Arduino-DMX-512-Tester-and-Controller/Arduino-DMX-512-Tester-and-Controller-LCD-20x4-Hardware/Documentacion/Contraste/Contrast PWM.png

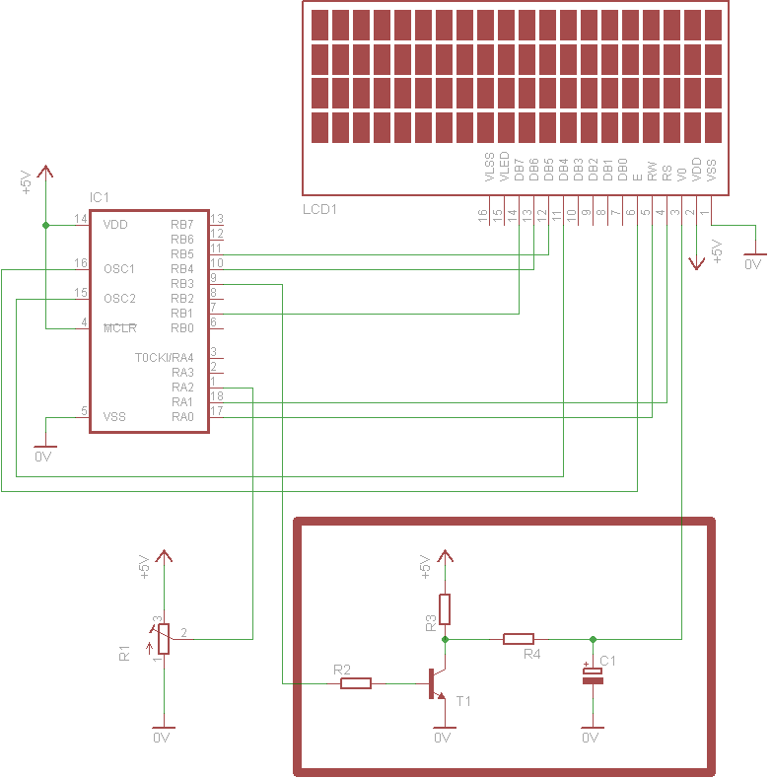
Documentacion/Contraste/Contrast PWM.png
