Arduino-DMX-512-Tester-and-Controller/Arduino-DMX-512-Tester-and-Controller-LCD-20x4-Hardware/Documentacion/DMX Shield/DMXShieldSchema.png

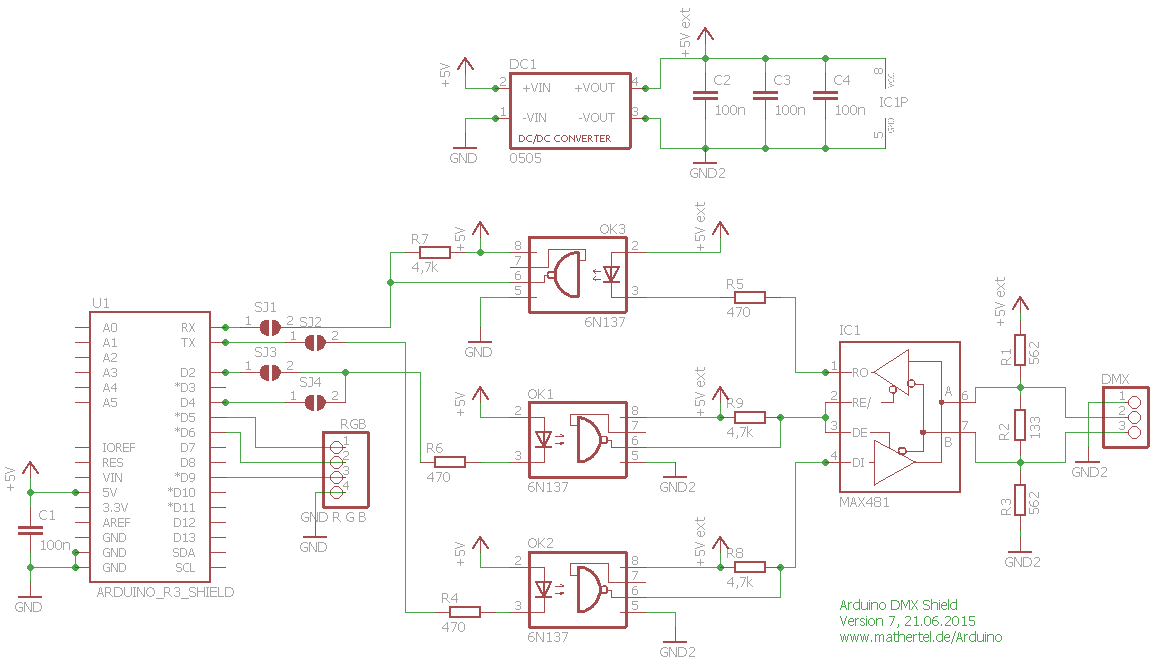
Documentacion/DMX Shield/DMXShieldSchema.png
