Arduino-DMX-512-Tester-and-Controller/Arduino-DMX-512-Tester-and-Controller-LCD-20x4-Hardware/Documentacion/Optoacoplado/DMXShieldSchema.png

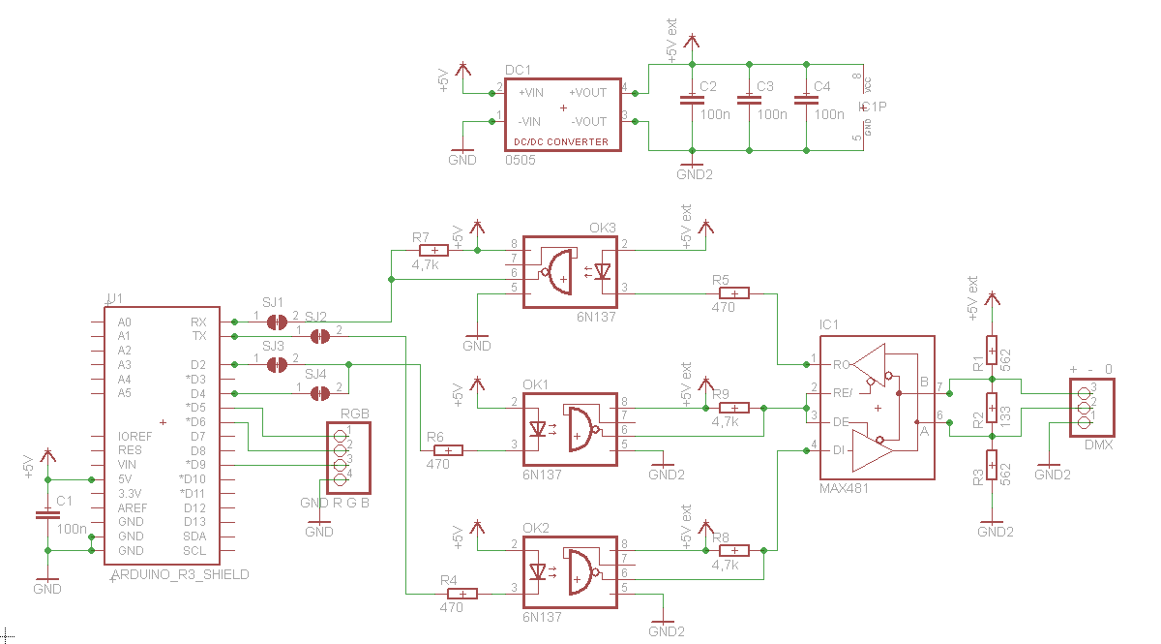
Documentacion/Optoacoplado/DMXShieldSchema.png
