Arduino-DMX-512-Tester-and-Controller/Arduino-DMX-512-Tester-and-Controller-LCD-20x4-Hardware/Documentacion/Teclado/Teclado diagrama.JPG

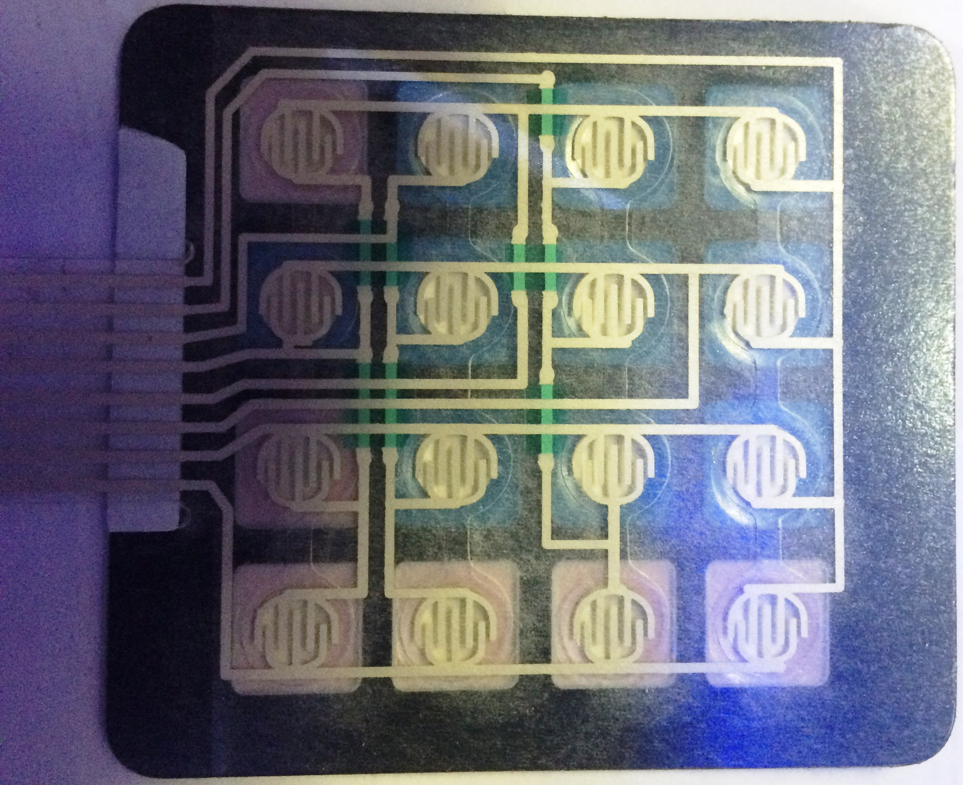
Documentacion/Teclado/Teclado diagrama.JPG
