Arduino-DMX-512-Tester-and-Controller/Arduino-DMX-512-Tester-and-Controller-LCD-20x4-Hardware/Documentacion/Teclado/teclado-4x4-alfanumerico pcb.jpg

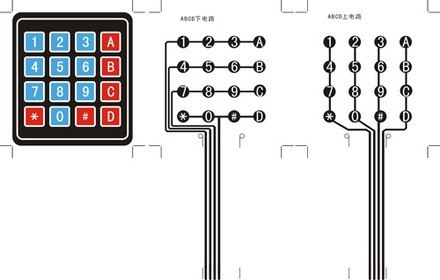
Documentacion/Teclado/teclado-4x4-alfanumerico pcb.jpg
