Arduino-DMX-512-Tester-and-Controller/Arduino-DMX-512-Tester-and-Controller-LCD-20x4-Hardware/Documentacion/Teclado/teclado-4x4-alfanumerico.jpg

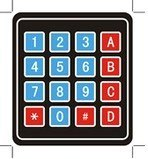
Documentacion/Teclado/teclado-4x4-alfanumerico.jpg
