Arduino-DMX-512-Tester-and-Controller/Arduino-DMX-512-Tester-and-Controller-LCD-20x4-Hardware/Social/Facebook/512 likes.PNG

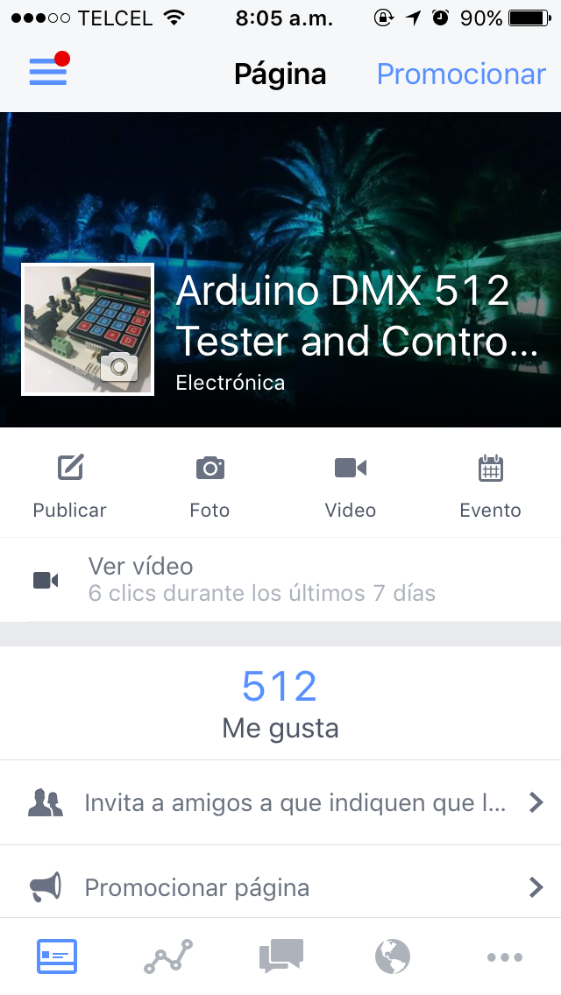
Social/Facebook/512 likes.PNG
