Arduino-DMX-512-Tester-and-Controller/Arduino-DMX-512-Tester-and-Controller-LCD-20x4-Hardware/Social/Hack a Day/HackaDay - Atmel Arduino 2.jpg

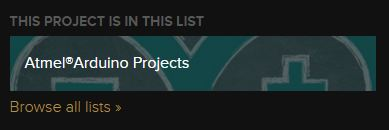
Social/Hack a Day/HackaDay - Atmel Arduino 2.jpg
