Arduino-DMX-512-Tester-and-Controller/Arduino-DMX-512-Tester-and-Controller-LCD-20x4-Hardware/Social/Makers/Alejandro Oteiza - España/18425617_912503192225845_1862307571_n.png

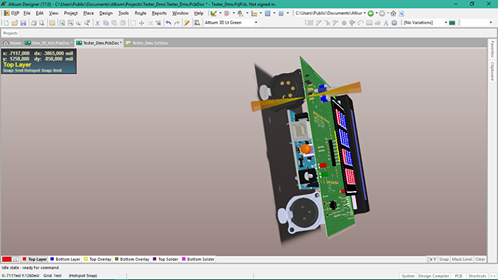
Social/Makers/Alejandro Oteiza - España/18425617_912503192225845_1862307571_n.png
