Arduino-DMX-512-Tester-and-Controller/Arduino-DMX-512-Tester-and-Controller-LCD-20x4-Hardware/Social/Makers/Alejandro Oteiza - España/18426019_912503318892499_1582437020_n.png

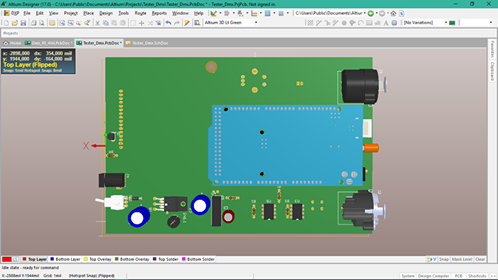
Social/Makers/Alejandro Oteiza - España/18426019_912503318892499_1582437020_n.png
