Arduino-DMX-512-Tester-and-Controller/Arduino-DMX-512-Tester-and-Controller-LCD-20x4-Hardware/Social/Makers/Alejandro Oteiza - España/19478004_941198602689637_196751368_n.jpg

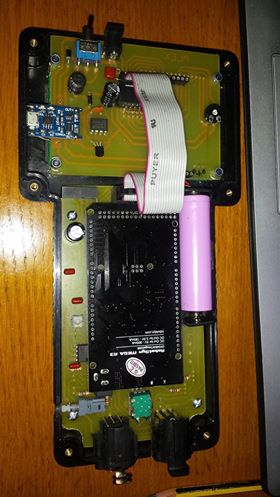
Social/Makers/Alejandro Oteiza - España/19478004_941198602689637_196751368_n.jpg
