Arduino-DMX-512-Tester-and-Controller/Arduino-DMX-512-Tester-and-Controller-LCD-20x4-Hardware/Social/Makers/Alejandro Oteiza - España/IMG_0107.jpg

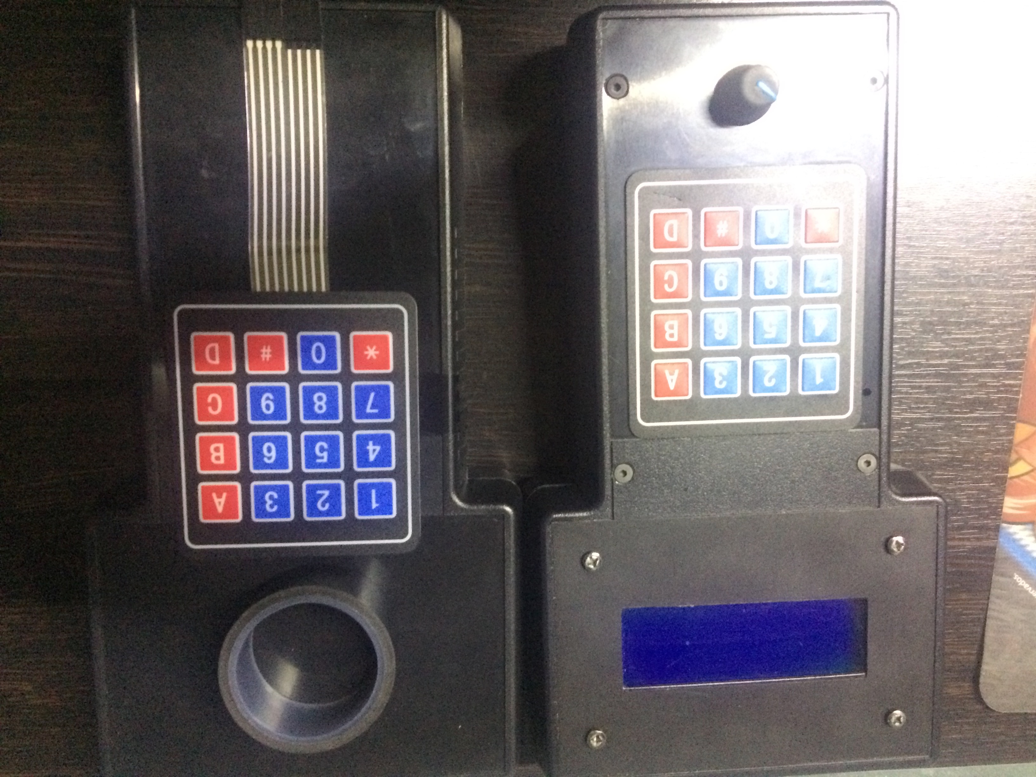
Social/Makers/Alejandro Oteiza - España/IMG_0107.jpg
