Arduino-DMX-512-Tester-and-Controller/Arduino-DMX-512-Tester-and-Controller-LCD-20x4-Hardware/Social/Makers/Magno Campos - Portugal/15725818_1213531232016235_1485832653_o.jpg

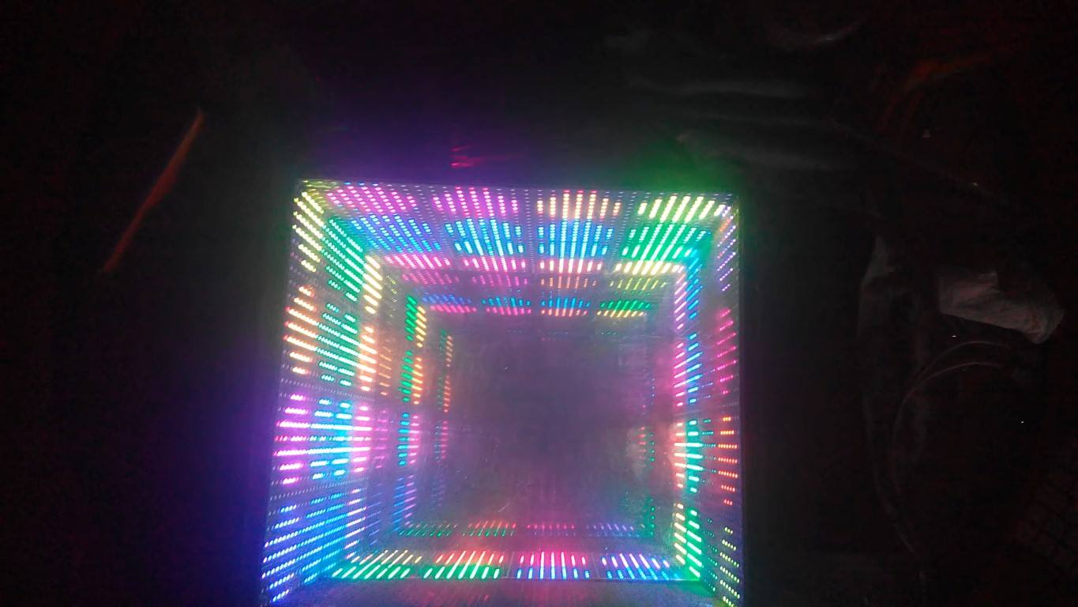
Social/Makers/Magno Campos - Portugal/15725818_1213531232016235_1485832653_o.jpg
