Arduino-DMX-512-Tester-and-Controller/Arduino-DMX-512-Tester-and-Controller-LCD-20x4-Hardware/Social/Makers/Magno Campos - Portugal/15725822_1213531238682901_1854752186_o.jpg

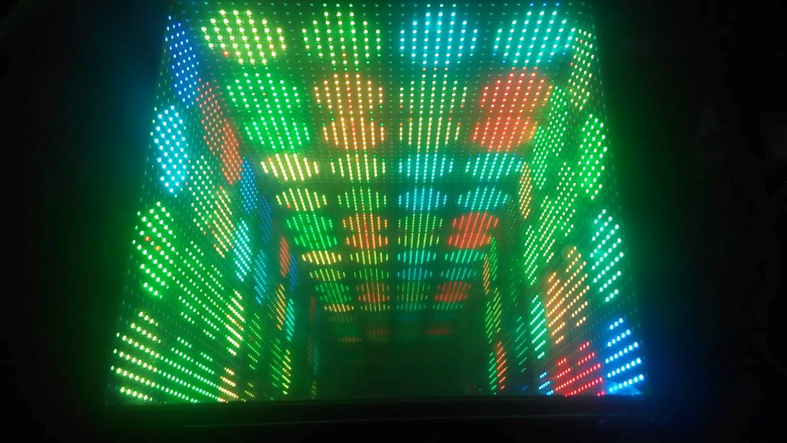
Social/Makers/Magno Campos - Portugal/15725822_1213531238682901_1854752186_o.jpg
