Arduino-DMX-512-Tester-and-Controller/Arduino-DMX-512-Tester-and-Controller-LCD-20x4-Hardware/Social/Makers/Magno Campos - Portugal/15725825_1213540395348652_77643821_o.jpg

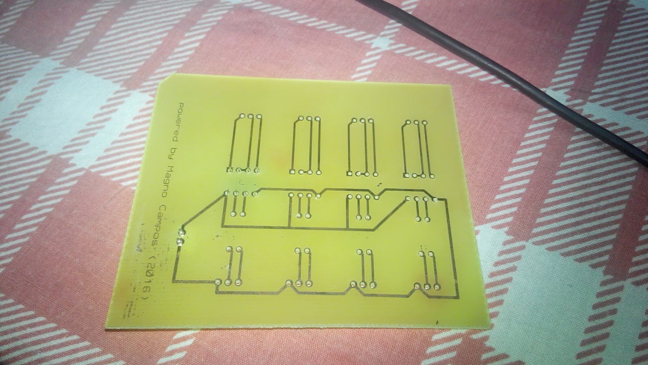
Social/Makers/Magno Campos - Portugal/15725825_1213540395348652_77643821_o.jpg
