Arduino-DMX-512-Tester-and-Controller/Arduino-DMX-512-Tester-and-Controller-LCD-20x4-Hardware/Social/Makers/Magno Campos - Portugal/15731043_1213531242016234_359219261_n.jpg

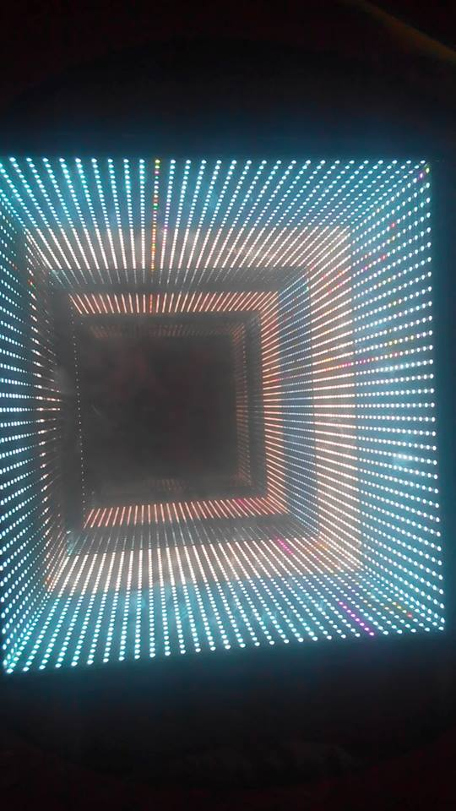
Social/Makers/Magno Campos - Portugal/15731043_1213531242016234_359219261_n.jpg
