Arduino-DMX-512-Tester-and-Controller/Arduino-DMX-512-Tester-and-Controller-LCD-20x4-Hardware/Social/Makers/Magno Campos - Portugal/15731415_1213531228682902_2014972093_n.jpg

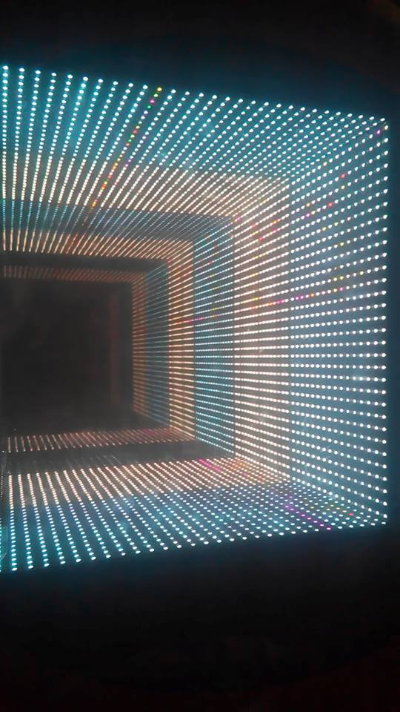
Social/Makers/Magno Campos - Portugal/15731415_1213531228682902_2014972093_n.jpg
