Arduino-DMX-512-Tester-and-Controller/Arduino-DMX-512-Tester-and-Controller-LCD-20x4-Hardware/Social/Makers/Magno Campos - Portugal/15776203_1213536035349088_677702162_o.jpg

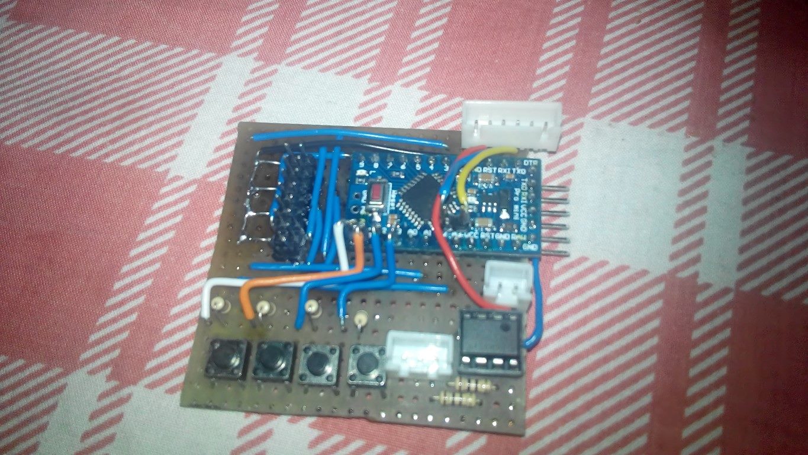
Social/Makers/Magno Campos - Portugal/15776203_1213536035349088_677702162_o.jpg
