Arduino-DMX-512-Tester-and-Controller/Arduino-DMX-512-Tester-and-Controller-LCD-20x4-Hardware/Social/Makers/Magno Campos - Portugal/15782216_1213531235349568_45997107_n.jpg

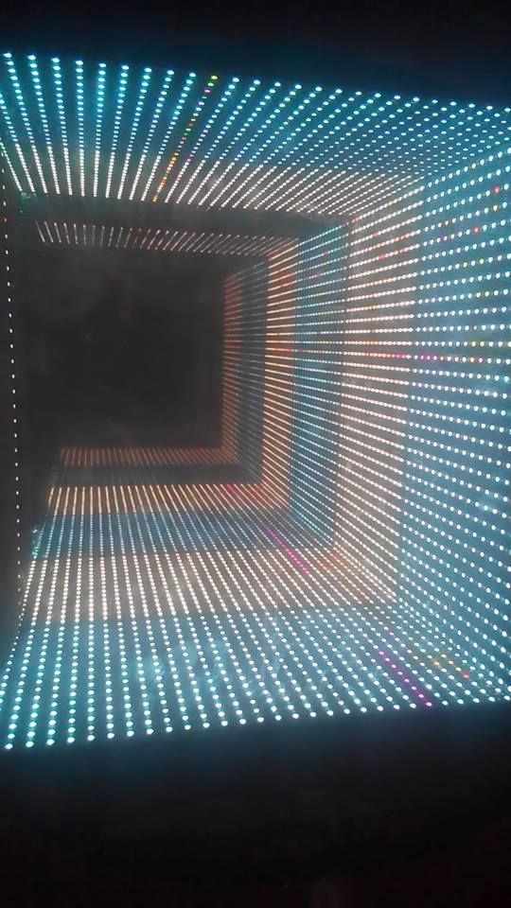
Social/Makers/Magno Campos - Portugal/15782216_1213531235349568_45997107_n.jpg
